kaushleshchandel/boondock/mediakit/images/boondock_how_it_works.PNG

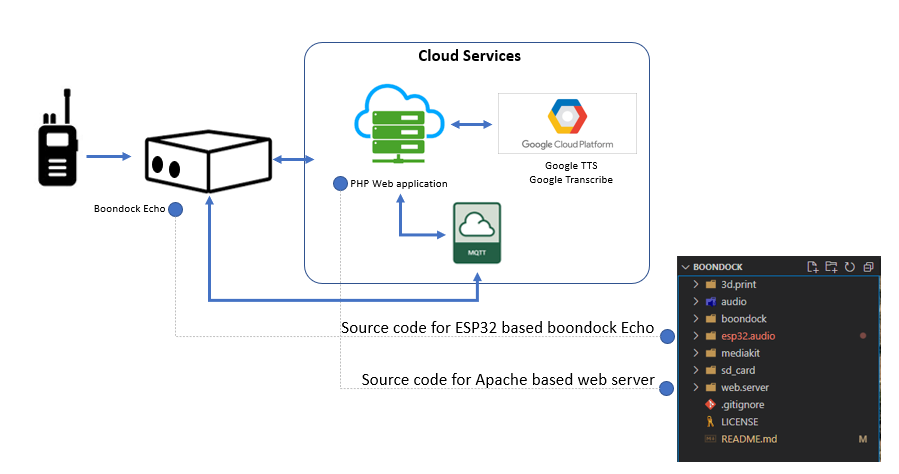
mediakit/images/boondock_how_it_works.PNG
