kaushleshchandel/boondock/mediakit/images/Hughes_LHHTopo.png

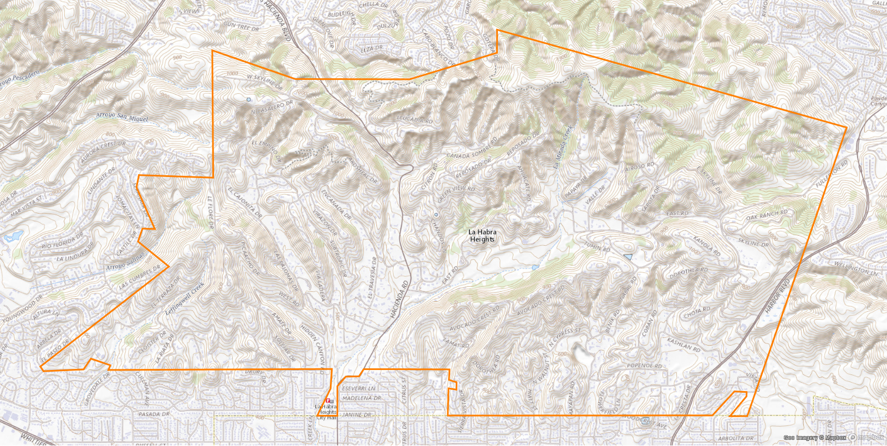
mediakit/images/Hughes_LHHTopo.png
