kaushleshchandel/boondock/mediakit/images/thumb-programming.png

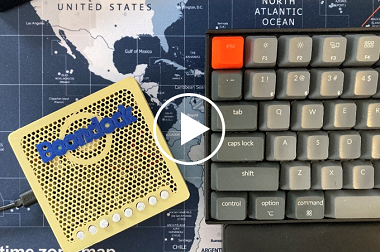
mediakit/images/thumb-programming.png
