kaushleshchandel/boondock/mediakit/images/thumb-server.png

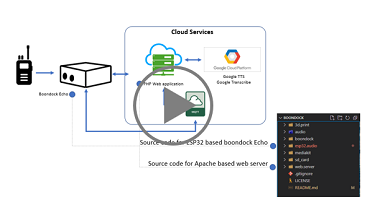
mediakit/images/thumb-server.png
